y-samy/aur24-fp-console/Mechanical/Final Project fab Assem.SLDASM

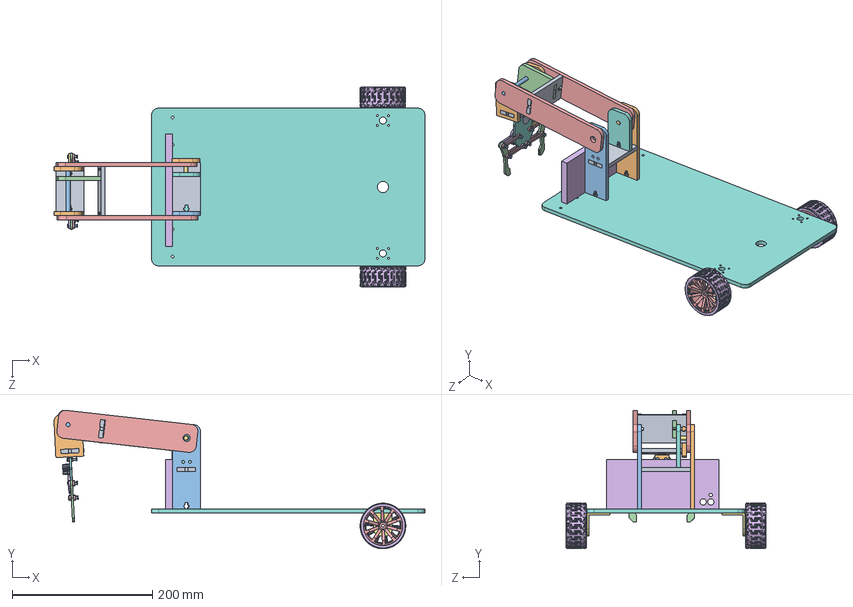
[picture p6: CAD file, 2024-11-01]
Mechanical/Final Project fab Assem.SLDASM
529.2 x 197.5 x 284.6 mm
Chassis
DC Motor Bracket x 2
65mm tire x 2
blue_wheel_frame x 2
motor_adapter x 2
Pillar 1
Pillar2
Bridge 1 x 2
Pillar 3
Rod 1
Phone
Pillar 4 x 2
Pillar 5
Rod 2
Pillar 6 x 2
Gripper Base
