y-samy/aur24-fp-console/Mechanical/blue_wheel_frame.SLDPRT

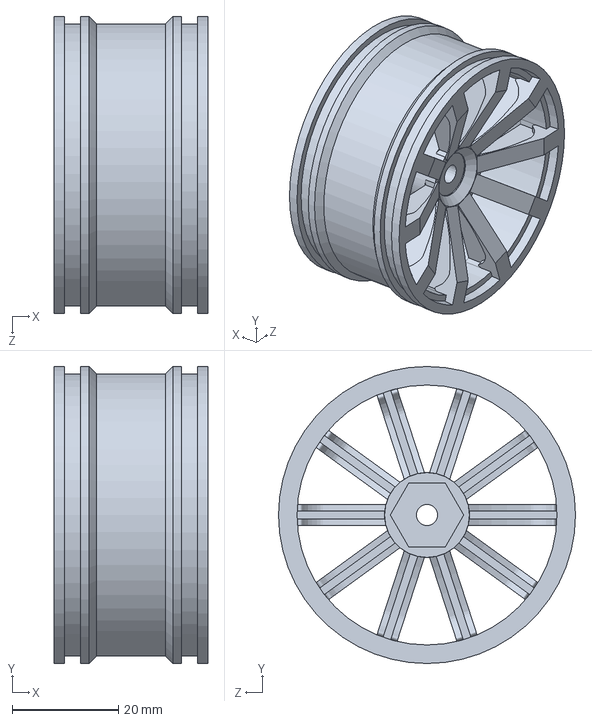
[picture p20: CAD file, 2024-11-01]
Mechanical/blue_wheel_frame.SLDPRT
29.0 x 56.0 x 56.0 mm
