y-samy/aur24-fp-console/Mechanical/65mm tire.SLDPRT

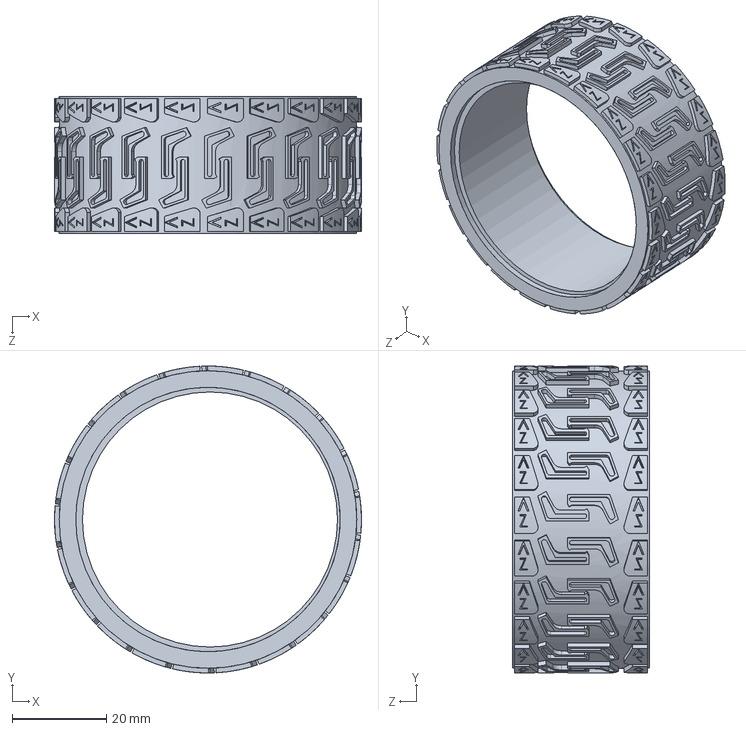
[picture p21: CAD file, 2024-11-01]
Mechanical/65mm tire.SLDPRT
65.0 x 65.0 x 29.0 mm
