y-samy/aur24-fp-console/Mechanical/Part3-3.SLDPRT

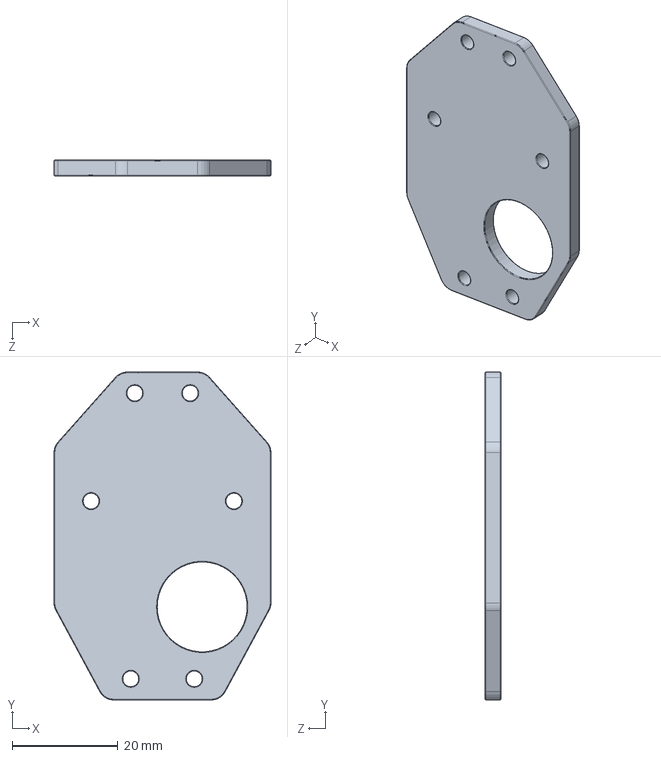
[picture p22: CAD file, 2024-11-01]
Mechanical/Part3-3.SLDPRT
41.0 x 62.0 x 3.00 mm
