y-samy/aur24-fp-console/Mechanical/Caster Ball Wheel.STEP

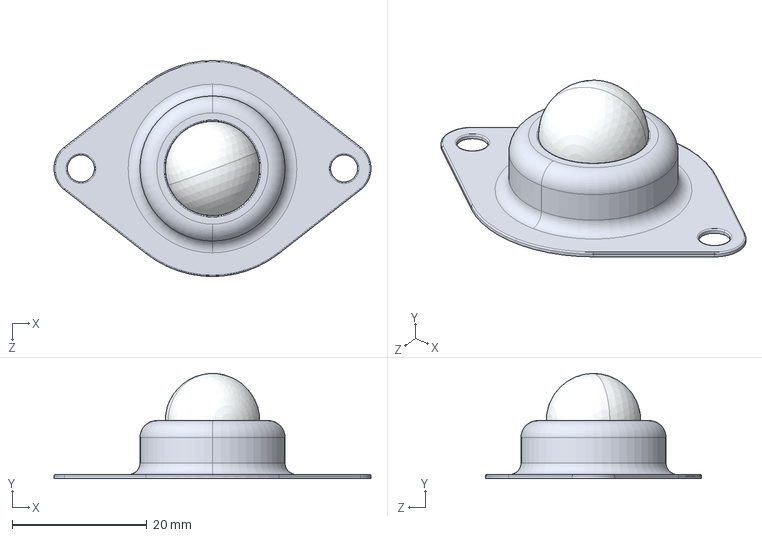
[picture p23: CAD file, 2024-11-01]
Mechanical/Caster Ball Wheel.STEP
47.0 x 15.6 x 32.0 mm
Wheel''s Body
Ball
