y-samy/aur24-fp-console/Mechanical/Rod 1.SLDPRT

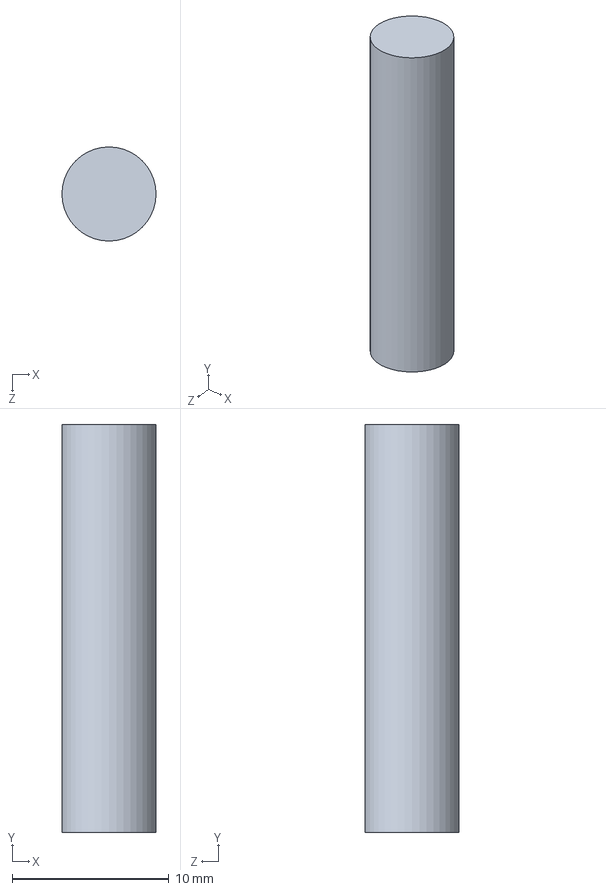
[picture p24: CAD file, 2024-11-01]
Mechanical/Rod 1.SLDPRT
6.00 x 26.0 x 6.00 mm
