y-samy/aur24-fp-console/Mechanical/Bridge 1.SLDPRT

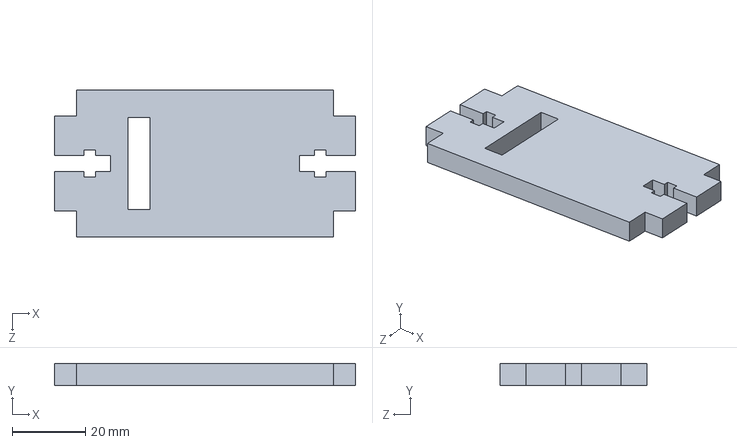
[picture p25: CAD file, 2024-11-01]
Mechanical/Bridge 1.SLDPRT
82.0 x 6.00 x 40.0 mm
