y-samy/aur24-fp-console/Mechanical/Part1-1.SLDPRT

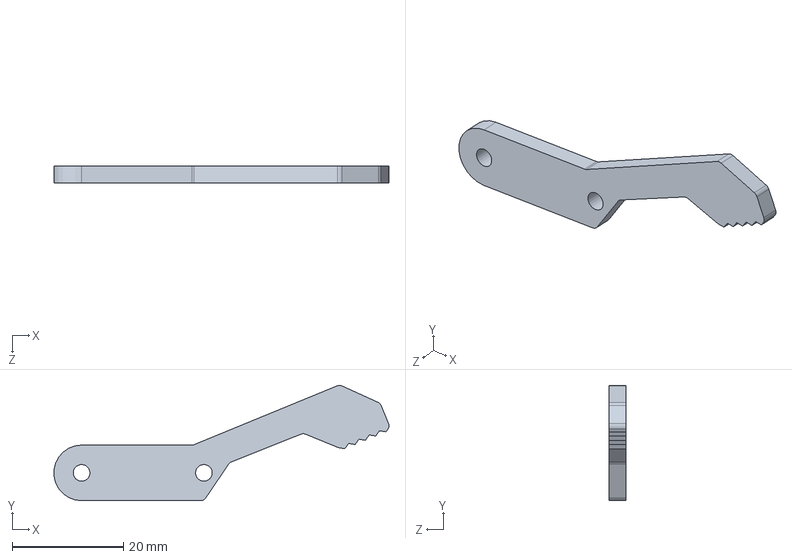
[picture p26: CAD file, 2024-11-01]
Mechanical/Part1-1.SLDPRT
60.3 x 20.7 x 3.00 mm
