y-samy/aur24-fp-console/Mechanical/motor_adapter.SLDPRT

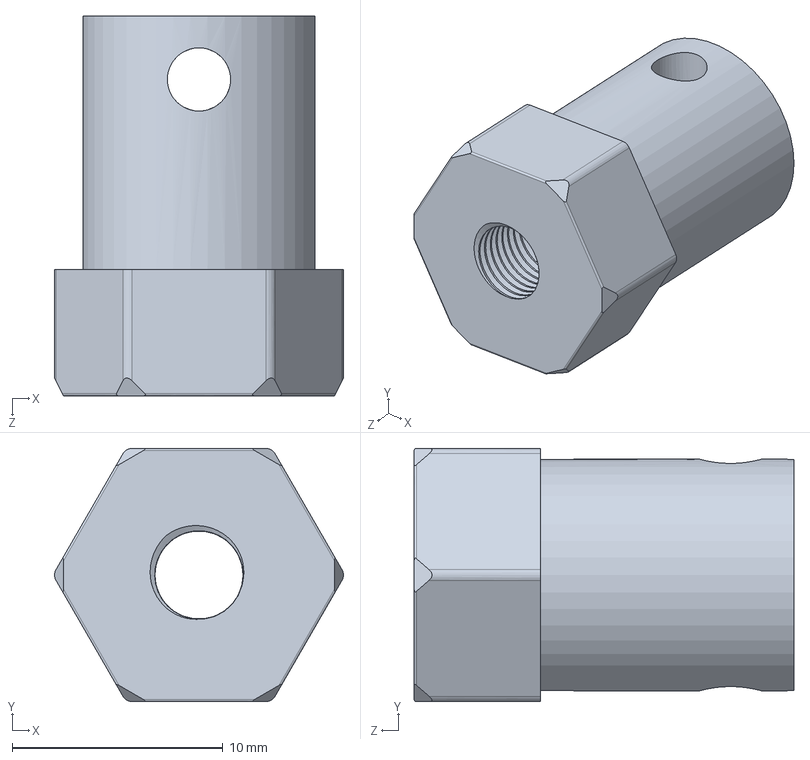
[picture p27: CAD file, 2024-11-01]
Mechanical/motor_adapter.SLDPRT
13.7 x 12.0 x 18.0 mm
