y-samy/aur24-fp-console/Mechanical/Phone.SLDPRT

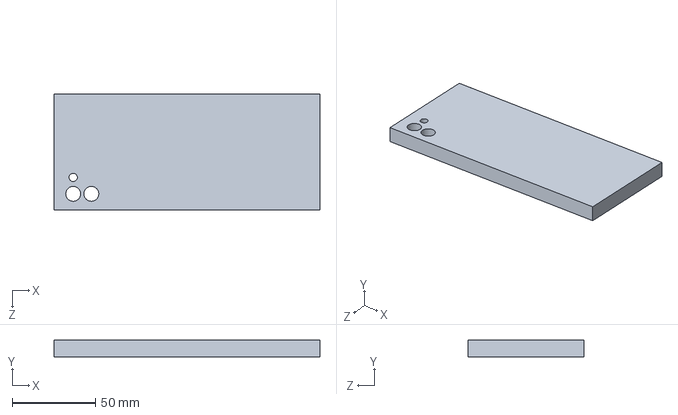
[picture p28: CAD file, 2024-11-01]
Mechanical/Phone.SLDPRT
160.0 x 10.0 x 70.0 mm
