y-samy/aur24-fp-console/Mechanical/Part2-2.SLDPRT

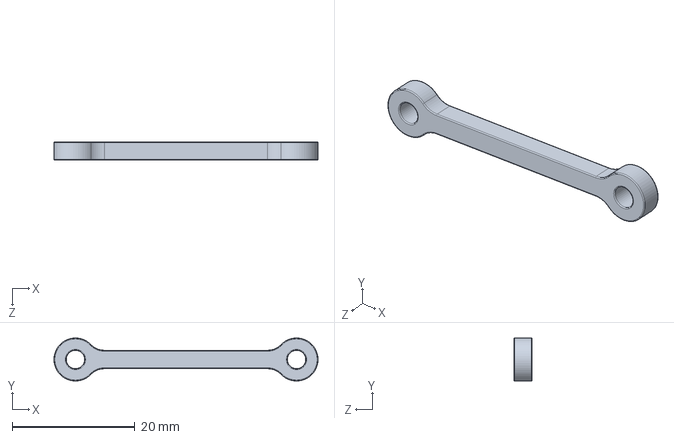
[picture p29: CAD file, 2024-11-01]
Mechanical/Part2-2.SLDPRT
43.0 x 7.00 x 3.00 mm
