y-samy/aur24-fp-console/Mechanical/Pillar 5.SLDPRT

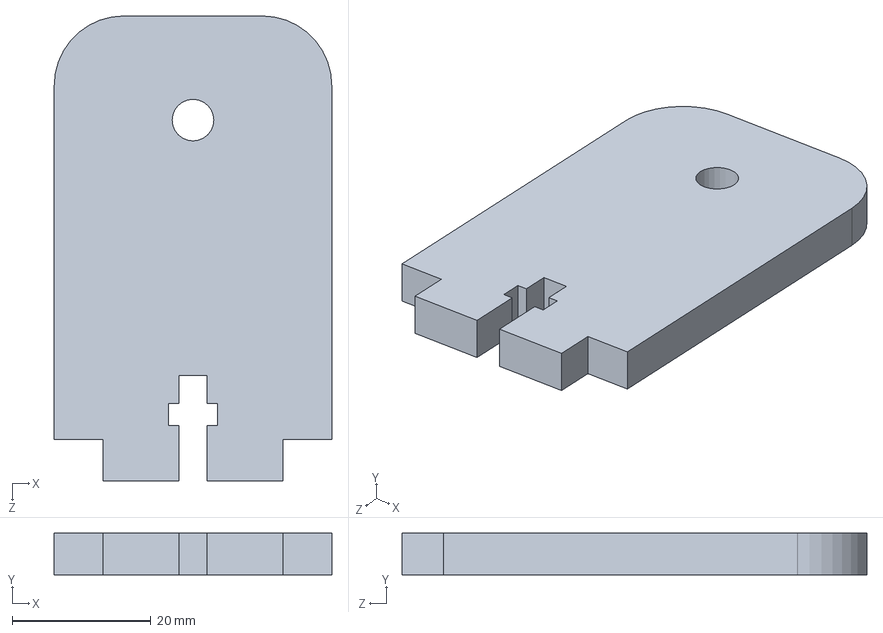
[picture p30: CAD file, 2024-11-01]
Mechanical/Pillar 5.SLDPRT
40.0 x 6.00 x 67.0 mm
