y-samy/aur24-fp-console/Mechanical/Pillar 4.SLDPRT

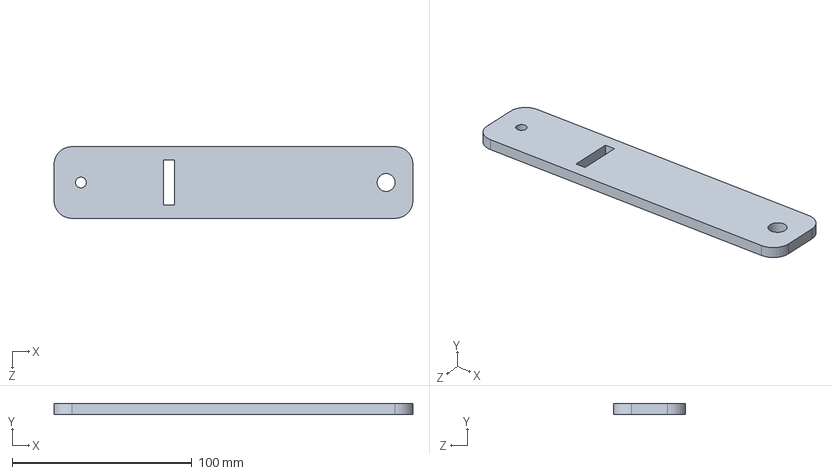
[picture p31: CAD file, 2024-11-01]
Mechanical/Pillar 4.SLDPRT
200.0 x 6.00 x 40.0 mm
