y-samy/aur24-fp-console/Mechanical/Geared DC motor with encoder - TS-25GA370H (12V 150RPM).step

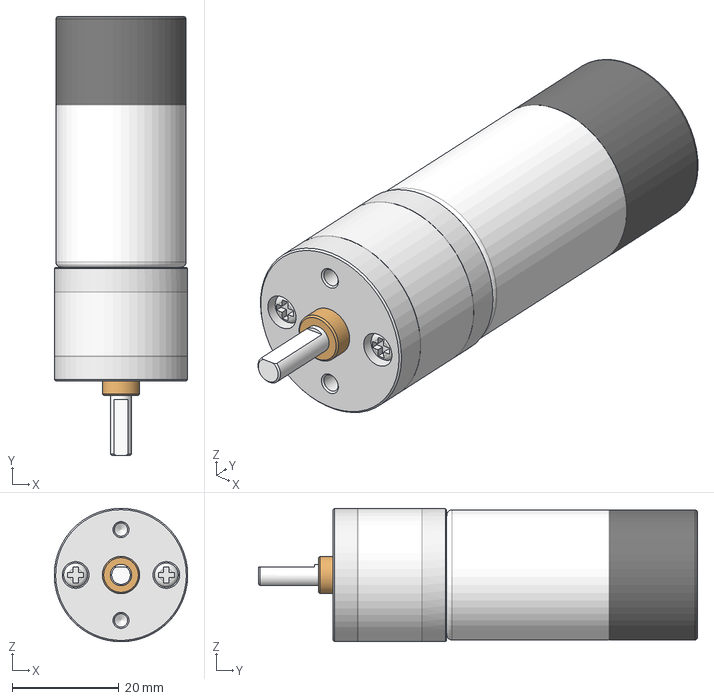
[picture p32: CAD file, 2024-11-01]
Mechanical/Geared DC motor with encoder - TS-25GA370H (12V 150RPM).step
25.0 x 82.2 x 25.0 mm
